A2J2123/ECE-298-Reservoir-Simulator/Hardware/Production Check/Pre-Production(1).PNG

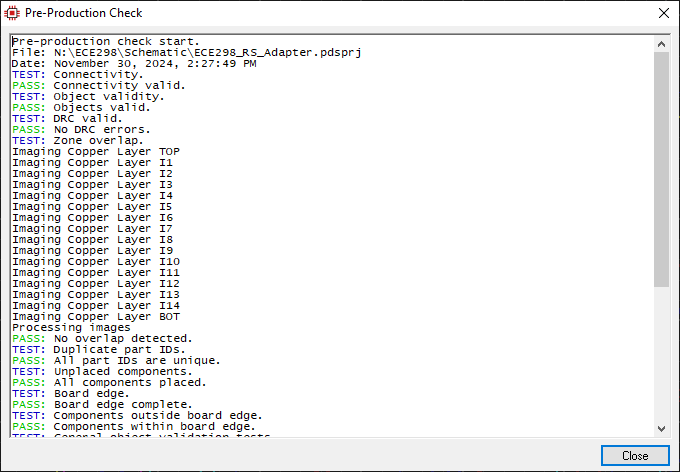
Hardware/Production Check/Pre-Production(1).PNG
